Friedjof/GlowLight/media/images/diagrams/classes.png

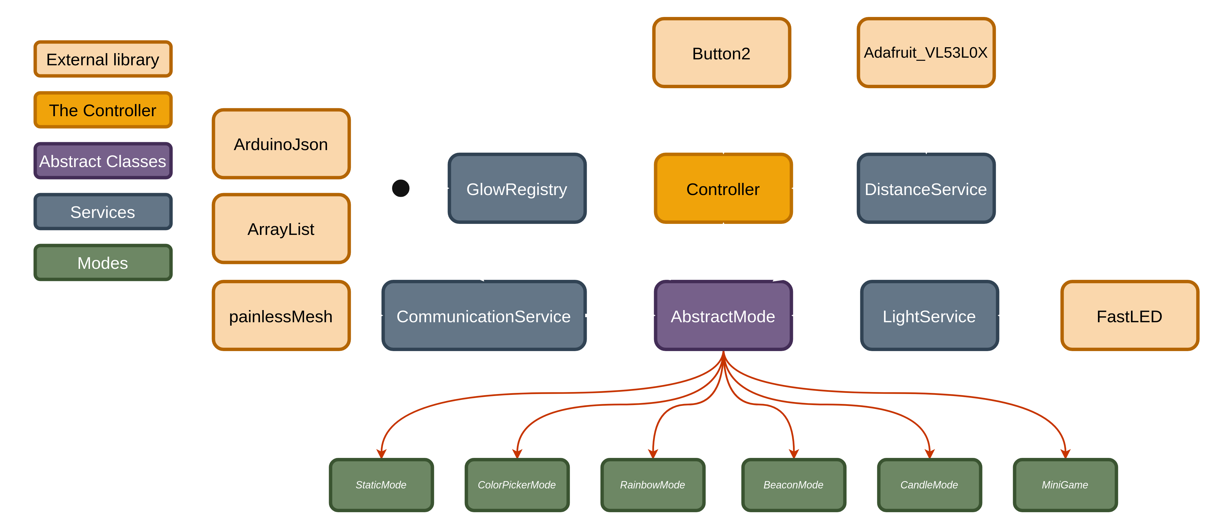
media/images/diagrams/classes.png
