Friedjof/GlowLight/media/images/components/button_sensor_esp32c3.jpg

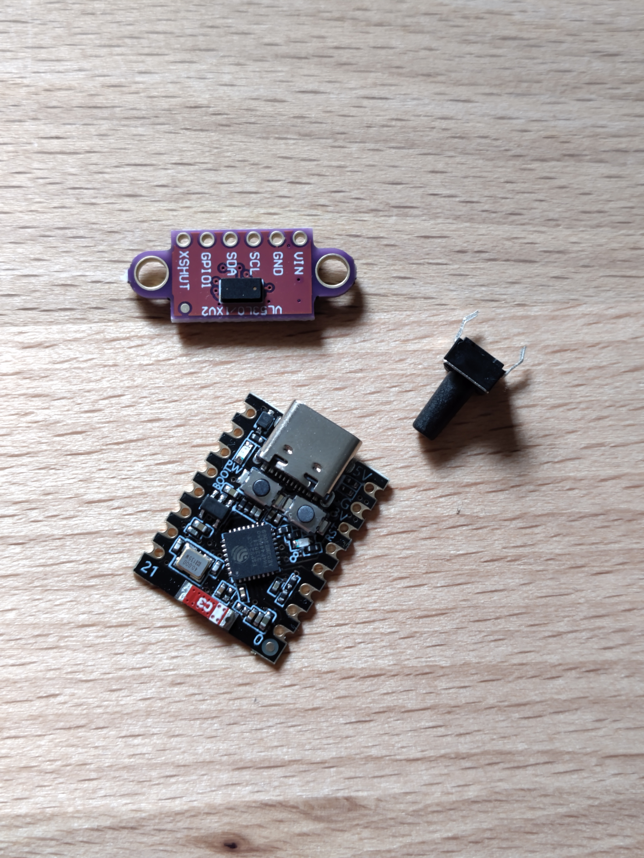
media/images/components/button_sensor_esp32c3.jpg
