Friedjof/GlowLight/media/images/printing/table_lamp_components.jpg

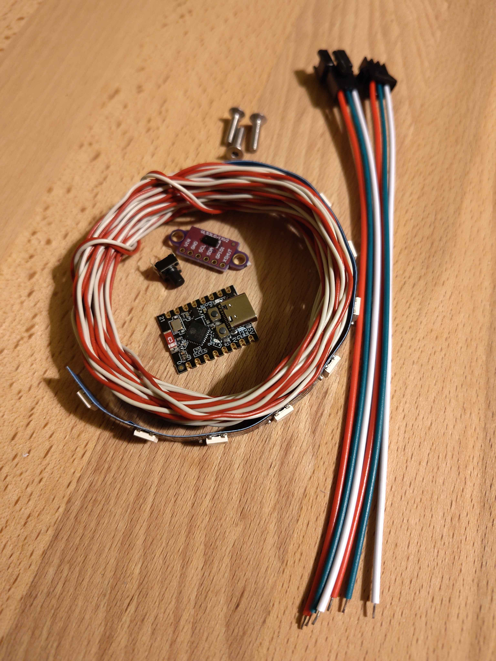
media/images/printing/table_lamp_components.jpg
